nickbild/vectron_handheld/media/prototype.jpg

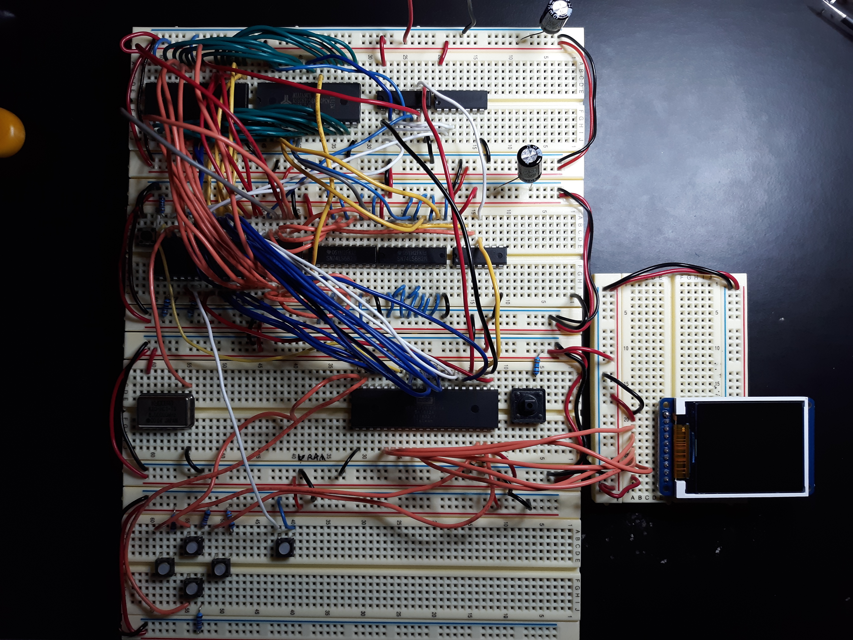
media/prototype.jpg
